drmendel/pictemp_net/firmware/TCPIP/App/GenericTCPServer.c

#define __GENERICTCPSERVER_C

#include "TCPIPConfig.h"

#if defined(STACK_USE_GENERIC_TCP_SERVER_EXAMPLE)

#include "TCPIP Stack/TCPIP.h"
#include "temperature_sensor.h"

// Defines which port the server will listen on
#define SERVER_PORT	2000

void GenericTCPServer(void)
{
	BYTE AppBuffer[32];
    unsigned char TMP_Buffer[TMP_Buffer_Size];           // Buffer to store TMP string
    WORD AB_Length;
	WORD wMaxGet, wMaxPut;
    unsigned int TMP_Inited = 0;
    unsigned int i; 
	static TCP_SOCKET	MySocket;
	static enum _TCPServerState
	{
		SM_HOME = 0,
		SM_LISTENING,
        SM_CLOSING,
	} TCPServerState = SM_HOME;

	switch(TCPServerState)
	{
		case SM_HOME:
			// Allocate a socket for this server to listen and accept connections on
			MySocket = TCPOpen(0, TCP_OPEN_SERVER, SERVER_PORT, TCP_PURPOSE_GENERIC_TCP_SERVER);
			if(MySocket == INVALID_SOCKET) return;
			TCPServerState = SM_LISTENING;
			break;

		case SM_LISTENING:
			// See if anyone is connected to us
			if(!TCPIsConnected(MySocket)) return;
            if(!TMP_Inited)
            {
                TMP_Init();
                TMP_Inited = 1;
            }
            
            // Figure out how many bytes have been received and how many we can transmit.
			wMaxGet = TCPIsGetReady(MySocket);	// Get TCP RX FIFO byte count
			wMaxPut = TCPIsPutReady(MySocket);	// Get TCP TX FIFO free space
    
            if(wMaxGet > 0) // We have incoming data
            {
                // Process all bytes that we can
                WORD Read_Length = (wMaxGet > sizeof(AppBuffer)) ? sizeof(AppBuffer) : wMaxGet;
                AB_Length = TCPGetArray(MySocket, AppBuffer, Read_Length);
                
                
                for(i = 0; i < AB_Length; i++) {
                    
                    if(AppBuffer[i] != 'T' && AppBuffer[i] != 't') {             
                        TCPServerState = SM_CLOSING;
                        break;
                    }
                    // READ the temp sensor 
                    ADC_to_TMP(TMP_Buffer, TMP_Read());
                    // Put the data to the TX buffer
                    //          in this case the package is max. 10 bytes "-40.00 °C\0", "125.00 °C\0"
                    //          we do not need to chunk the buffer to smaller packets
                    TCPPutArray(MySocket, TMP_Buffer, strlen(TMP_Buffer));
                    TCPFlush(MySocket);     // Send data immediately
                }
			}
			break;

		case SM_CLOSING:
			// Close the socket connection.
            TCPClose(MySocket);
			TCPServerState = SM_HOME;
			break;
	}
}

#endif //#if defined(STACK_USE_GENERIC_TCP_SERVER_EXAMPLE)


/*********************************************************************
 *
 *	Generic TCP Server Example Application
 *  Module for Microchip TCP/IP Stack
 *   -Implements an example "ToUpper" TCP server on port 9760 and 
 *	  should be used as a basis for creating new TCP server 
 *    applications
 *
 *********************************************************************
 * FileName:        GenericTCPServer.c
 * Dependencies:    TCP
 * Processor:       PIC18, PIC24F, PIC24H, dsPIC30F, dsPIC33F, PIC32
 * Compiler:        Microchip C32 v1.05 or higher
 *					Microchip C30 v3.12 or higher
 *					Microchip C18 v3.30 or higher
 *					HI-TECH PICC-18 PRO 9.63PL2 or higher
 * Company:         Microchip Technology, Inc.
 *
 * Software License Agreement
 *
 * Copyright (C) 2002-2009 Microchip Technology Inc.  All rights
 * reserved.
 *
 * Microchip licenses to you the right to use, modify, copy, and
 * distribute:
 * (i)  the Software when embedded on a Microchip microcontroller or
 *      digital signal controller product ("Device") which is
 *      integrated into Licensee's product; or
 * (ii) ONLY the Software driver source files ENC28J60.c, ENC28J60.h,
 *		ENCX24J600.c and ENCX24J600.h ported to a non-Microchip device
 *		used in conjunction with a Microchip ethernet controller for
 *		the sole purpose of interfacing with the ethernet controller.
 *
 * You should refer to the license agreement accompanying this
 * Software for additional information regarding your rights and
 * obligations.
 *
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
 *
 * Author               Date    	Comment
 *~~~~~~~~~~~~~~~~~~~~~~~~~~~~~~~~~~~~~~~~~~~~~~~~~~~~~~~~~~~~~~~~~~~~
 * Howard Schlunder     10/19/06	Original
 * Microchip            08/11/10    Added ability to close session by
 *                                  pressing the ESCAPE key.
 *~~~~~~~~~~~~~~~~~~~~~~~~~~~~~~~~~~~~~~~~~~~~~~~~~~~~~~~~~~~~~~~~~~~~
 *
 * Description of how to run the demo:
 *   1) Connect the ethernet port of the programmed demo board to a 
 *        computer either directly or through a router.
 *   2) Determine the IP address of the demo board.  This can be done several
 *        different ways.
 *      a) If you are using a demo setup with an LCD display (e.g. Explorer 16
 *           or PICDEM.net 2), the IP address should be displayed on the second
 *           line of the display.
 *      b) Open the Microchip Ethernet Device Discoverer from the start menu.
 *           Press the "Discover Devices" button to see the addresses and host
 *           names of all devices with the Announce Protocol enabled on your
 *           network.  You may have to configure your computer's firewall to 
 *           prevent it from blocking UDP port 30303 for this solution.
 *      c) If your board is connected directly with your computer with a
 *           crossover cable: 
 *              1) Open a command/DOS prompt and type 'ipconfig'.  Find the 
 *                   network adaptor that is connected to the board.  The IP
 *                   address of the board is located in the 'Default Gateway'
 *                   field
 *              2) Open up the network status for the network adaptor that
 *                   connects the two devices.  This can be done by right clicking
 *                   on the network connection icon in the network settings folder 
 *                   and select 'status' from the menu. Find the 'Default Gateway'
 *                   field.
 *   3) Open a command/DOS prompt.  Type "telnet ip_address 9760" where
 *        ip_address is the IP address that you got from step 2.
 *   4) As you type characters, they will be echoed back in your command prompt
 *        window in UPPER CASE.
 *   5) Press Escape to end the demo.
 *
 ********************************************************************/


/*****************************************************************************
  Function:
	void GenericTCPServer(void)

  Summary:
	Implements a simple ToUpper TCP Server.

  Description:
	This function implements a simple TCP server.  The function is invoked
	periodically by the stack to listen for incoming connections.  When a 
	connection is made, the server reads all incoming data, transforms it
	to uppercase, and echos it back.
	
	This example can be used as a model for many TCP server applications.

  Precondition:
	TCP is initialized.

  Parameters:
	None

  Returns:
  	None
  ***************************************************************************/
