drmendel/pictemp_net/firmware/TCPIP/App/MainDemo.c

/*********************************************************************
 *
 *  Main Application Entry Point and TCP/IP Stack Demo
 *  Module for Microchip TCP/IP Stack
 *   -Demonstrates how to call and use the Microchip TCP/IP stack
 *	 -Reference: Microchip TCP/IP Stack Help (TCPIP Stack Help.chm)
 *
 *********************************************************************
 * FileName:        MainDemo.c
 * Dependencies:    TCPIP.h
 * Processor:       PIC18, PIC24F, PIC24H, dsPIC30F, dsPIC33F, PIC32
 * Compiler:        Microchip C32 v1.11b or higher
 *					Microchip C30 v3.24 or higher
 *					Microchip C18 v3.36 or higher
 * Company:         Microchip Technology, Inc.
 *
 * Software License Agreement
 *
 * Copyright (C) 2002-2010 Microchip Technology Inc.  All rights
 * reserved.
 *
 * Microchip licenses to you the right to use, modify, copy, and
 * distribute:
 * (i)  the Software when embedded on a Microchip microcontroller or
 *      digital signal controller product ("Device") which is
 *      integrated into Licensee's product; or
 * (ii) ONLY the Software driver source files ENC28J60.c, ENC28J60.h,
 *		ENCX24J600.c and ENCX24J600.h ported to a non-Microchip device
 *		used in conjunction with a Microchip ethernet controller for
 *		the sole purpose of interfacing with the ethernet controller.
 *
 * You should refer to the license agreement accompanying this
 * Software for additional information regarding your rights and
 * obligations.
 *
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
 * File Description:
 * Change History:
 * Rev   Description
 * ----  -----------------------------------------
 * 1.0   Initial release
 * V5.36 ---- STACK_USE_MPFS support has been removed 
 ********************************************************************/
/*
 * This macro uniquely defines this file as the main entry point.
 * There should only be one such definition in the entire project,
 * and this file must define the AppConfig variable as described below.
 */
#define THIS_IS_STACK_APPLICATION

// Include all headers for any enabled TCPIP Stack functions
#include "TCPIP Stack/TCPIP.h"

#if defined(STACK_USE_ZEROCONF_LINK_LOCAL)
#include "TCPIP Stack/ZeroconfLinkLocal.h"
#endif
#if defined(STACK_USE_ZEROCONF_MDNS_SD)
#include "TCPIP Stack/ZeroconfMulticastDNS.h"
#endif

// Include functions specific to this stack application
#include "MainDemo.h"

// Used for Wi-Fi assertions
#define WF_MODULE_NUMBER   WF_MODULE_MAIN_DEMO

// Declare AppConfig structure and some other supporting stack variables
APP_CONFIG AppConfig;
static unsigned short wOriginalAppConfigChecksum;	// Checksum of the ROM defaults for AppConfig
BYTE AN0String[8];

// Use UART2 instead of UART1 for stdout (printf functions).  Explorer 16 
// serial port hardware is on PIC UART2 module.
#if defined(EXPLORER_16) || defined(PIC24FJ256DA210_DEV_BOARD)
	int __C30_UART = 2;
#endif


// Private helper functions.
// These may or may not be present in all applications.
static void InitAppConfig(void);
static void InitializeBoard(void);
static void ProcessIO(void);
#if defined(WF_CS_TRIS)
    static void WF_Connect(void);
#endif

//
// PIC18 Interrupt Service Routines
// 
// NOTE: Several PICs, including the PIC18F4620 revision A3 have a RETFIE FAST/MOVFF bug
// The interruptlow keyword is used to work around the bug when using C18
#if defined(__18CXX)
	#if defined(HI_TECH_C)
	void interrupt low_priority LowISR(void)
	#else
	#pragma interruptlow LowISR
	void LowISR(void)
	#endif
	{
	    TickUpdate();
	}
	
	#if defined(HI_TECH_C)
	void interrupt HighISR(void)
	#else
	#pragma interruptlow HighISR
	void HighISR(void)
	#endif
	{
	    #if defined(STACK_USE_UART2TCP_BRIDGE)
			UART2TCPBridgeISR();
		#endif

		#if defined(WF_CS_TRIS)
			WFEintISR();
		#endif // WF_CS_TRIS
	}

	#if !defined(HI_TECH_C)
	#pragma code lowVector=0x18
	void LowVector(void){_asm goto LowISR _endasm}
	#pragma code highVector=0x8
	void HighVector(void){_asm goto HighISR _endasm}
	#pragma code // Return to default code section
	#endif

// C30 and C32 Exception Handlers
// If your code gets here, you either tried to read or write
// a NULL pointer, or your application overflowed the stack
// by having too many local variables or parameters declared.
#elif defined(__C30__)
	void _ISR __attribute__((__no_auto_psv__)) _AddressError(void)
	{
	    Nop();
		Nop();
	}
	void _ISR __attribute__((__no_auto_psv__)) _StackError(void)
	{
	    Nop();
		Nop();
	}
	
#elif defined(__C32__)
	void _general_exception_handler(unsigned cause, unsigned status)
	{
		Nop();
		Nop();
	}
#endif


//
// Main application entry point.
//
#if defined(__18CXX)
void main(void)
#else
int main(void)
#endif
{
	static DWORD t = 0;
	static DWORD dwLastIP = 0;
	#if defined(WF_USE_POWER_SAVE_FUNCTIONS)
	BOOL  PsPollEnabled;
	BOOL  psConfDone = FALSE;
	#endif

	// Initialize application specific hardware
	InitializeBoard();

	#if defined(USE_LCD)
	// Initialize and display the stack version on the LCD
	LCDInit();
	DelayMs(100);
	strcpypgm2ram((char*)LCDText, "TCPStack " TCPIP_STACK_VERSION "  "
		"                ");
	LCDUpdate();
	#endif

	// Initialize stack-related hardware components that may be 
	// required by the UART configuration routines
    TickInit();
	#if defined(STACK_USE_MPFS2)
	MPFSInit();
	#endif

	// Initialize Stack and application related NV variables into AppConfig.
	InitAppConfig();

    // Initiates board setup process if button is depressed 
	// on startup
    if(BUTTON0_IO == 0u)
    {
		#if defined(EEPROM_CS_TRIS) || defined(SPIFLASH_CS_TRIS)
		// Invalidate the EEPROM contents if BUTTON0 is held down for more than 4 seconds
		DWORD StartTime = TickGet();
		LED_PUT(0x00);
				
		while(BUTTON0_IO == 0u)
		{
			if(TickGet() - StartTime > 4*TICK_SECOND)
			{
				#if defined(EEPROM_CS_TRIS)
			    XEEBeginWrite(0x0000);
			    XEEWrite(0xFF);
			    XEEWrite(0xFF);
			    XEEEndWrite();
			    #elif defined(SPIFLASH_CS_TRIS)
			    SPIFlashBeginWrite(0x0000);
			    SPIFlashWrite(0xFF);
			    SPIFlashWrite(0xFF);
			    #endif
			    
				#if defined(STACK_USE_UART)
				putrsUART("\r\n\r\nBUTTON0 held for more than 4 seconds.  Default settings restored.\r\n\r\n");
				#endif

				LED_PUT(0x0F);
				while((LONG)(TickGet() - StartTime) <= (LONG)(9*TICK_SECOND/2));
				LED_PUT(0x00);
				while(BUTTON0_IO == 0u);
				Reset();
				break;
			}
		}
		#endif

		#if defined(STACK_USE_UART)
        DoUARTConfig();
		#endif
    }

	// Initialize core stack layers (MAC, ARP, TCP, UDP) and
	// application modules (HTTP, SNMP, etc.)
    StackInit();

    #if defined(WF_CS_TRIS)
    WF_Connect();
    #endif

	// Initialize any application-specific modules or functions/
	// For this demo application, this only includes the
	// UART 2 TCP Bridge
	#if defined(STACK_USE_UART2TCP_BRIDGE)
	UART2TCPBridgeInit();
	#endif

	#if defined(STACK_USE_ZEROCONF_LINK_LOCAL)
    ZeroconfLLInitialize();
	#endif

	#if defined(STACK_USE_ZEROCONF_MDNS_SD)
	mDNSInitialize(MY_DEFAULT_HOST_NAME);
	mDNSServiceRegister(
		(const char *) "DemoWebServer",	// base name of the service
		"_http._tcp.local",			    // type of the service
		80,				                // TCP or UDP port, at which this service is available
		((const BYTE *)"path=/index.htm"),	// TXT info
		1,								    // auto rename the service when if needed
		NULL,							    // no callback function
		NULL							    // no application context
		);

    mDNSMulticastFilterRegister();			
	#endif

	// Now that all items are initialized, begin the co-operative
	// multitasking loop.  This infinite loop will continuously 
	// execute all stack-related tasks, as well as your own
	// application's functions.  Custom functions should be added
	// at the end of this loop.
    // Note that this is a "co-operative mult-tasking" mechanism
    // where every task performs its tasks (whether all in one shot
    // or part of it) and returns so that other tasks can do their
    // job.
    // If a task needs very long time to do its job, it must be broken
    // down into smaller pieces so that other tasks can have CPU time.    
    
    while(1)
    {
	#if defined(WF_USE_POWER_SAVE_FUNCTIONS)
		if (!psConfDone && WFisConnected()) {	
			PsPollEnabled = (MY_DEFAULT_PS_POLL == WF_ENABLED);
			if (!PsPollEnabled) {	 
				/* disable low power (PS-Poll) mode */
				#if defined(STACK_USE_UART)
				putrsUART("Disable PS-Poll\r\n");		 
				#endif
				WF_PsPollDisable();
			} else {
				/* Enable low power (PS-Poll) mode */
				#if defined(STACK_USE_UART)
				putrsUART("Enable PS-Poll\r\n");		
				#endif
				WF_PsPollEnable(TRUE);
			}	
			psConfDone = TRUE;
		}
	#endif
        // Blink LED0 (right most one) every second.
        if(TickGet() - t >= TICK_SECOND/2ul)
        {
            t = TickGet();
            LED0_IO ^= 1;
        }

        // This task performs normal stack task including checking
        // for incoming packet, type of packet and calling
        // appropriate stack entity to process it.
        StackTask();

        // This tasks invokes each of the core stack application tasks
        StackApplications();

        #if defined(STACK_USE_ZEROCONF_LINK_LOCAL)
		ZeroconfLLProcess();
        #endif

        #if defined(STACK_USE_ZEROCONF_MDNS_SD)
        mDNSProcess();
		// Use this function to exercise service update function
		// HTTPUpdateRecord();
        #endif

		// Process application specific tasks here.
		// For this demo app, this will include the Generic TCP 
		// client and servers, and the SNMP, Ping, and SNMP Trap
		// demos.  Following that, we will process any IO from
		// the inputs on the board itself.
		// Any custom modules or processing you need to do should
		// go here.
		#if defined(STACK_USE_GENERIC_TCP_CLIENT_EXAMPLE)
		GenericTCPClient();
		#endif
		
		#if defined(STACK_USE_GENERIC_TCP_SERVER_EXAMPLE)
		GenericTCPServer();
		#endif
		
		#if defined(STACK_USE_SMTP_CLIENT)
		SMTPDemo();
		#endif
		
		#if defined(STACK_USE_ICMP_CLIENT)
		PingDemo();
		#endif
		
		#if defined(STACK_USE_SNMP_SERVER) && !defined(SNMP_TRAP_DISABLED)
		//User should use one of the following SNMP demo
		// This routine demonstrates V1 or V2 trap formats with one variable binding.
		SNMPTrapDemo();
		
		#if defined(SNMP_STACK_USE_V2_TRAP) || defined(SNMP_V1_V2_TRAP_WITH_SNMPV3)
		//This routine provides V2 format notifications with multiple (3) variable bindings
		//User should modify this routine to send v2 trap format notifications with the required varbinds.
		//SNMPV2TrapDemo();
		#endif 
		if(gSendTrapFlag)
			SNMPSendTrap();
		#endif
		
		#if defined(STACK_USE_BERKELEY_API)
		BerkeleyTCPClientDemo();
		BerkeleyTCPServerDemo();
		BerkeleyUDPClientDemo();
		#endif

		ProcessIO();

        // If the local IP address has changed (ex: due to DHCP lease change)
        // write the new IP address to the LCD display, UART, and Announce 
        // service
		if(dwLastIP != AppConfig.MyIPAddr.Val)
		{
			dwLastIP = AppConfig.MyIPAddr.Val;
			
			#if defined(STACK_USE_UART)
				putrsUART((ROM char*)"\r\nNew IP Address: ");
			#endif

			DisplayIPValue(AppConfig.MyIPAddr);

			#if defined(STACK_USE_UART)
				putrsUART((ROM char*)"\r\n");
			#endif


			#if defined(STACK_USE_ANNOUNCE)
				AnnounceIP();
			#endif

            #if defined(STACK_USE_ZEROCONF_MDNS_SD)
				mDNSFillHostRecord();
			#endif
		}
	}
}

#if defined(WF_CS_TRIS)
/*****************************************************************************
 * FUNCTION: WF_Connect
 *
 * RETURNS:  None
 *
 * PARAMS:   None
 *
 *  NOTES:   Connects to an 802.11 network.  Customize this function as needed 
 *           for your application.
 *****************************************************************************/
static void WF_Connect(void)
{
    UINT8 ConnectionProfileID;
    UINT8 channelList[] = MY_DEFAULT_CHANNEL_LIST;
    
    /* create a Connection Profile */
    WF_CPCreate(&ConnectionProfileID);

    #if defined(STACK_USE_UART)
    putrsUART("Set SSID (");
    putsUART(AppConfig.MySSID);
    putrsUART(")\r\n");
    #endif
    WF_CPSetSsid(ConnectionProfileID, 
                 AppConfig.MySSID, 
                 AppConfig.SsidLength);

    #if defined(STACK_USE_UART)
    putrsUART("Set Network Type\r\n");
	#endif
    WF_CPSetNetworkType(ConnectionProfileID, MY_DEFAULT_NETWORK_TYPE);
    
	#if defined(STACK_USE_UART)
	putrsUART("Set Scan Type\r\n");
	#endif
    WF_CASetScanType(MY_DEFAULT_SCAN_TYPE);
    
    #if defined(STACK_USE_UART)
    putrsUART("Set Channel List\r\n");
    #endif    
    WF_CASetChannelList(channelList, sizeof(channelList));
    
    #if defined(STACK_USE_UART)
    putrsUART("Set list retry count\r\n");
    #endif
    // The Retry Count parameter tells the WiFi Connection manager how many attempts to make when trying
    // to connect to an existing network.  In the Infrastructure case, the default is to retry forever so that
    // if the AP is turned off or out of range, the radio will continue to attempt a connection until the
    // AP is eventually back on or in range.  In the Adhoc case, the default is to retry 3 times since the 
    // purpose of attempting to establish a network in the Adhoc case is only to verify that one does not
    // initially exist.  If the retry count was set to WF_RETRY_FOREVER in the AdHoc mode, an AdHoc network
    // would never be established.  The constants MY_DEFAULT_LIST_RETRY_COUNT_ADHOC and 
    // MY_DEFAULT_LIST_RETRY_COUNT_INFRASTRUCTURE have been created specifically for the June 2011 MAL release.
    #if defined(EZ_CONFIG_STORE)
        if (AppConfig.networkType == WF_ADHOC)
            WF_CASetListRetryCount(MY_DEFAULT_LIST_RETRY_COUNT_ADHOC);
        else
            WF_CASetListRetryCount(MY_DEFAULT_LIST_RETRY_COUNT_INFRASTRUCTURE);
    #else
        #if (MY_DEFAULT_NETWORK_TYPE == WF_ADHOC)
            WF_CASetListRetryCount(MY_DEFAULT_LIST_RETRY_COUNT_ADHOC);
        #else
            WF_CASetListRetryCount(MY_DEFAULT_LIST_RETRY_COUNT_INFRASTRUCTURE);
        #endif
    #endif
    

    #if defined(STACK_USE_UART)        
    putrsUART("Set Event Notify\r\n");    
    #endif
    WF_CASetEventNotificationAction(MY_DEFAULT_EVENT_NOTIFICATION_LIST);
    
    #if defined(STACK_USE_UART)
    putrsUART("Set Beacon Timeout\r\n");
    #endif
    WF_CASetBeaconTimeout(40);
    
    /* Set Security */
    #if (MY_DEFAULT_WIFI_SECURITY_MODE == WF_SECURITY_OPEN)
        #if defined(STACK_USE_UART)
        putrsUART("Set Security (Open)\r\n");
        #endif
    #elif (MY_DEFAULT_WIFI_SECURITY_MODE == WF_SECURITY_WEP_40)
        #if defined(STACK_USE_UART)
        putrsUART("Set Security (WEP40)\r\n");
        #endif
    #elif (MY_DEFAULT_WIFI_SECURITY_MODE == WF_SECURITY_WEP_104)
        #if defined(STACK_USE_UART)
        putrsUART("Set Security (WEP104)\r\n");
        #endif
    #elif MY_DEFAULT_WIFI_SECURITY_MODE == WF_SECURITY_WPA_WITH_KEY 
        #if defined(STACK_USE_UART)
        putrsUART("Set Security (WPA with key)\r\n");
        #endif
    #elif MY_DEFAULT_WIFI_SECURITY_MODE == WF_SECURITY_WPA2_WITH_KEY 
        #if defined(STACK_USE_UART)
        putrsUART("Set Security (WPA2 with key)\r\n");
        #endif
    #elif MY_DEFAULT_WIFI_SECURITY_MODE == WF_SECURITY_WPA_WITH_PASS_PHRASE
        #if defined(STACK_USE_UART)
        putrsUART("Set Security (WPA with pass phrase)\r\n");
        #endif
    #elif MY_DEFAULT_WIFI_SECURITY_MODE == WF_SECURITY_WPA2_WITH_PASS_PHRASE
        #if defined(STACK_USE_UART)
        putrsUART("Set Security (WPA2 with pass phrase)\r\n");    
        #endif
    #elif MY_DEFAULT_WIFI_SECURITY_MODE == WF_SECURITY_WPA_AUTO_WITH_KEY
        #if defined(STACK_USE_UART)
        putrsUART("Set Security (WPA with key, auto-select)\r\n");
        #endif
    #elif MY_DEFAULT_WIFI_SECURITY_MODE == WF_SECURITY_WPA_AUTO_WITH_PASS_PHRASE
        #if defined(STACK_USE_UART)
        putrsUART("Set Security (WPA with pass phrase, auto-select)\r\n");
        #endif
    #endif /* MY_DEFAULT_WIFI_SECURITY_MODE */

    WF_CPSetSecurity(ConnectionProfileID,
                     AppConfig.SecurityMode,
                     AppConfig.WepKeyIndex,   /* only used if WEP enabled */
                     AppConfig.SecurityKey,
                     AppConfig.SecurityKeyLength);
    #if defined(STACK_USE_UART)                     
    putrsUART("Start WiFi Connect\r\n");        
    #endif
    WF_CMConnect(ConnectionProfileID);
}   
#endif /* WF_CS_TRIS */

// Writes an IP address to the LCD display and the UART as available
void DisplayIPValue(IP_ADDR IPVal)
{
//	printf("%u.%u.%u.%u", IPVal.v[0], IPVal.v[1], IPVal.v[2], IPVal.v[3]);
#if defined (__dsPIC33E__) || defined (__PIC24E__)
	static BYTE IPDigit[4];    					/* Needs to be declared as static to avoid the array getting optimized by C30 v3.30 compiler for dsPIC33E/PIC24E. 
												   Otherwise the LCD displays corrupted IP address on Explorer 16. To be fixed in the future compiler release*/
#else
    BYTE IPDigit[4];
#endif
	BYTE i;
#ifdef USE_LCD
	BYTE j;
	BYTE LCDPos=16;
#endif

	for(i = 0; i < sizeof(IP_ADDR); i++)
	{
	    uitoa((WORD)IPVal.v[i], IPDigit);

		#if defined(STACK_USE_UART)
			putsUART((char *) IPDigit);
		#endif

		#ifdef USE_LCD
			for(j = 0; j < strlen((char*)IPDigit); j++)
			{
				LCDText[LCDPos++] = IPDigit[j];
			}
			if(i == sizeof(IP_ADDR)-1)
				break;
			LCDText[LCDPos++] = '.';
		#else
			if(i == sizeof(IP_ADDR)-1)
				break;
		#endif

		#if defined(STACK_USE_UART)
			while(BusyUART());
			WriteUART('.');
		#endif
	}

	#ifdef USE_LCD
		if(LCDPos < 32u)
			LCDText[LCDPos] = 0;
		LCDUpdate();
	#endif
}

// Processes A/D data from the potentiometer
static void ProcessIO(void)
{
#if defined(__C30__) || defined(__C32__)
    // Convert potentiometer result into ASCII string
    uitoa((WORD)ADC1BUF0, AN0String);
#else
    // AN0 should already be set up as an analog input
    ADCON0bits.GO = 1;

    // Wait until A/D conversion is done
    while(ADCON0bits.GO);

	// AD converter errata work around (ex: PIC18F87J10 A2)
	#if !defined(__18F87J50) && !defined(_18F87J50) && !defined(__18F87J11) && !defined(_18F87J11) 
	{
		BYTE temp = ADCON2;
		ADCON2 |= 0x7;	// Select Frc mode by setting ADCS0/ADCS1/ADCS2
		ADCON2 = temp;
	}
	#endif

    // Convert 10-bit value into ASCII string
    uitoa(*((WORD*)(&ADRESL)), AN0String);
#endif
}


/****************************************************************************
  Function:
    static void InitializeBoard(void)

  Description:
    This routine initializes the hardware.  It is a generic initialization
    routine for many of the Microchip development boards, using definitions
    in HardwareProfile.h to determine specific initialization.

  Precondition:
    None

  Parameters:
    None - None

  Returns:
    None

  Remarks:
    None
  ***************************************************************************/
static void InitializeBoard(void)
{	
	// LEDs
	LED0_TRIS = 0;
	LED1_TRIS = 0;
	LED2_TRIS = 0;
	LED3_TRIS = 0;
	LED4_TRIS = 0;
	LED5_TRIS = 0;
	LED6_TRIS = 0;
	LED7_TRIS = 0;
	LED_PUT(0x00);

#if defined(__18CXX)
	// Enable 4x/5x/96MHz PLL on PIC18F87J10, PIC18F97J60, PIC18F87J50, etc.
    OSCTUNE = 0x40;

	// Set up analog features of PORTA

	// PICDEM.net 2 board has POT on AN2, Temp Sensor on AN3
	#if defined(PICDEMNET2)
		ADCON0 = 0x09;		// ADON, Channel 2
		ADCON1 = 0x0B;		// Vdd/Vss is +/-REF, AN0, AN1, AN2, AN3 are analog
	#elif defined(PICDEMZ)
		ADCON0 = 0x81;		// ADON, Channel 0, Fosc/32
		ADCON1 = 0x0F;		// Vdd/Vss is +/-REF, AN0, AN1, AN2, AN3 are all digital
	#elif defined(__18F87J11) || defined(_18F87J11) || defined(__18F87J50) || defined(_18F87J50)
		ADCON0 = 0x01;		// ADON, Channel 0, Vdd/Vss is +/-REF
		WDTCONbits.ADSHR = 1;
		ANCON0 = 0xFC;		// AN0 (POT) and AN1 (temp sensor) are anlog
		ANCON1 = 0xFF;
		WDTCONbits.ADSHR = 0;		
	#else
		ADCON0 = 0x01;		// ADON, Channel 0
		ADCON1 = 0x0E;		// Vdd/Vss is +/-REF, AN0 is analog
	#endif
	ADCON2 = 0xBE;		// Right justify, 20TAD ACQ time, Fosc/64 (~21.0kHz)


    // Enable internal PORTB pull-ups
    INTCON2bits.RBPU = 0;

	// Configure USART
    TXSTA = 0x20;
    RCSTA = 0x90;

	// See if we can use the high baud rate setting
	#if ((GetPeripheralClock()+2*BAUD_RATE)/BAUD_RATE/4 - 1) <= 255
		SPBRG = (GetPeripheralClock()+2*BAUD_RATE)/BAUD_RATE/4 - 1;
		TXSTAbits.BRGH = 1;
	#else	// Use the low baud rate setting
		SPBRG = (GetPeripheralClock()+8*BAUD_RATE)/BAUD_RATE/16 - 1;
	#endif


	// Enable Interrupts
	RCONbits.IPEN = 1;		// Enable interrupt priorities
    INTCONbits.GIEH = 1;
    INTCONbits.GIEL = 1;

    // Do a calibration A/D conversion
	#if defined(__18F87J10) || defined(__18F86J15) || defined(__18F86J10) || defined(__18F85J15) || defined(__18F85J10) || defined(__18F67J10) || defined(__18F66J15) || defined(__18F66J10) || defined(__18F65J15) || defined(__18F65J10) || defined(__18F97J60) || defined(__18F96J65) || defined(__18F96J60) || defined(__18F87J60) || defined(__18F86J65) || defined(__18F86J60) || defined(__18F67J60) || defined(__18F66J65) || defined(__18F66J60) || \
	     defined(_18F87J10) ||  defined(_18F86J15) || defined(_18F86J10)  ||  defined(_18F85J15) ||  defined(_18F85J10) ||  defined(_18F67J10) ||  defined(_18F66J15) ||  defined(_18F66J10) ||  defined(_18F65J15) ||  defined(_18F65J10) ||  defined(_18F97J60) ||  defined(_18F96J65) ||  defined(_18F96J60) ||  defined(_18F87J60) ||  defined(_18F86J65) ||  defined(_18F86J60) ||  defined(_18F67J60) ||  defined(_18F66J65) ||  defined(_18F66J60)
		ADCON0bits.ADCAL = 1;
	    ADCON0bits.GO = 1;
		while(ADCON0bits.GO);
		ADCON0bits.ADCAL = 0;
	#elif defined(__18F87J11) || defined(__18F86J16) || defined(__18F86J11) || defined(__18F67J11) || defined(__18F66J16) || defined(__18F66J11) || \
		   defined(_18F87J11) ||  defined(_18F86J16) ||  defined(_18F86J11) ||  defined(_18F67J11) ||  defined(_18F66J16) ||  defined(_18F66J11) || \
		  defined(__18F87J50) || defined(__18F86J55) || defined(__18F86J50) || defined(__18F67J50) || defined(__18F66J55) || defined(__18F66J50) || \
		   defined(_18F87J50) ||  defined(_18F86J55) ||  defined(_18F86J50) ||  defined(_18F67J50) ||  defined(_18F66J55) ||  defined(_18F66J50)
		ADCON1bits.ADCAL = 1;
	    ADCON0bits.GO = 1;
		while(ADCON0bits.GO);
		ADCON1bits.ADCAL = 0;
	#endif

#else	// 16-bit C30 and and 32-bit C32
	#if defined(__PIC32MX__)
	{
		// Enable multi-vectored interrupts
		INTEnableSystemMultiVectoredInt();
		
		// Enable optimal performance
		SYSTEMConfigPerformance(GetSystemClock());
		mOSCSetPBDIV(OSC_PB_DIV_1);				// Use 1:1 CPU Core:Peripheral clocks
		
		// Disable JTAG port so we get our I/O pins back, but first
		// wait 50ms so if you want to reprogram the part with 
		// JTAG, you'll still have a tiny window before JTAG goes away.
		// The PIC32 Starter Kit debuggers use JTAG and therefore must not 
		// disable JTAG.
		DelayMs(50);
		#if !defined(__MPLAB_DEBUGGER_PIC32MXSK) && !defined(__MPLAB_DEBUGGER_FS2)
			DDPCONbits.JTAGEN = 0;
		#endif
		LED_PUT(0x00);				// Turn the LEDs off
		
		CNPUESET = 0x00098000;		// Turn on weak pull ups on CN15, CN16, CN19 (RD5, RD7, RD13), which is connected to buttons on PIC32 Starter Kit boards
	}
	#endif

	#if defined(__dsPIC33F__) || defined(__PIC24H__)
		// Crank up the core frequency
		PLLFBD = 38;				// Multiply by 40 for 160MHz VCO output (8MHz XT oscillator)
		CLKDIV = 0x0000;			// FRC: divide by 2, PLLPOST: divide by 2, PLLPRE: divide by 2
	
		// Port I/O
		AD1PCFGHbits.PCFG23 = 1;	// Make RA7 (BUTTON1) a digital input
		AD1PCFGHbits.PCFG20 = 1;	// Make RA12 (INT1) a digital input for MRF24WB0M PICtail Plus interrupt

		// ADC
	    AD1CHS0 = 0;				// Input to AN0 (potentiometer)
		AD1PCFGLbits.PCFG5 = 0;		// Disable digital input on AN5 (potentiometer)
		AD1PCFGLbits.PCFG4 = 0;		// Disable digital input on AN4 (TC1047A temp sensor)


	#elif defined(__dsPIC33E__)||defined(__PIC24E__)

		// Crank up the core frequency
		PLLFBD = 38;				/* M  = 30	*/
		CLKDIVbits.PLLPOST = 0;		/* N1 = 2	*/
		CLKDIVbits.PLLPRE = 0;		/* N2 = 2	*/
		OSCTUN = 0;	
		
	    /*	Initiate Clock Switch to Primary
	     *	Oscillator with PLL (NOSC= 0x3)*/
	    __builtin_write_OSCCONH(0x03);		
		__builtin_write_OSCCONL(0x01);
		// Disable Watch Dog Timer
	    RCONbits.SWDTEN = 0;
		while (OSCCONbits.COSC != 0x3); 
		while (_LOCK == 0);			/* Wait for PLL lock at 60 MIPS */		
		// Port I/O
		ANSELAbits.ANSA7 = 0 ;   //Make RA7 (BUTTON1) a digital input
		#if defined ENC100_INTERFACE_MODE > 0
			ANSELEbits.ANSE0 = 0;      // Make these PMP pins as digital output when the interface is parallel.
			ANSELEbits.ANSE1 = 0;
			ANSELEbits.ANSE2 = 0;
			ANSELEbits.ANSE3 = 0;	
			ANSELEbits.ANSE4 = 0;
			ANSELEbits.ANSE5 = 0;
			ANSELEbits.ANSE6 = 0;
			ANSELEbits.ANSE7 = 0;	
			ANSELBbits.ANSB10 = 0;
			ANSELBbits.ANSB11 = 0;
			ANSELBbits.ANSB12 = 0;
			ANSELBbits.ANSB13 = 0;
			ANSELBbits.ANSB15 = 0;
		#endif

		ANSELEbits.ANSE8= 0 ;    // Make RE8(INT1) a digital input for ZeroG ZG2100M PICtail 
					
		AD1CHS0 = 0;		     // Input to AN0 (potentiometer)
		ANSELBbits.ANSB0= 1;     // Input to AN0 (potentiometer)
		ANSELBbits.ANSB5= 1;     // Disable digital input on AN5 (potentiometer)
		ANSELBbits.ANSB4= 1;     // Disable digital input on AN4 (TC1047A temp sensor)
					
		ANSELDbits.ANSD7 =0;     //  Digital Pin Selection for S3(Pin 83) and S4(pin 84).
		ANSELDbits.ANSD6 =0;
			
		ANSELGbits.ANSG6 =0;     // Enable Digital input for RG6 (SCK2)
		ANSELGbits.ANSG7 =0;     // Enable Digital input for RG7 (SDI2)
		ANSELGbits.ANSG8 =0;     // Enable Digital input for RG8 (SDO2)
		ANSELGbits.ANSG9 =0;     // Enable Digital input for RG9 (CS)
				
		#if defined ENC100_INTERFACE_MODE == 0	// SPI Interface, UART can be used for debugging. Not allowed for other interfaces.
			RPOR9 = 0x0300;          //RP101= U2TX
			RPINR19 = 0X0064;  		 //RP100= U2RX
		#endif

		#if defined WF_CS_TRIS
			RPINR1bits.INT3R = 30;
			WF_CS_IO = 1;
			WF_CS_TRIS = 0;		

		#endif

	#else	//defined(__PIC24F__) || defined(__PIC32MX__)
		#if defined(__PIC24F__)
			CLKDIVbits.RCDIV = 0;		// Set 1:1 8MHz FRC postscalar
		#endif
		
		// ADC
	    #if defined(__PIC24FJ256DA210__) || defined(__PIC24FJ256GB210__)
	    	// Disable analog on all pins
	    	ANSA = 0x0000;
	    	ANSB = 0x0000;
	    	ANSC = 0x0000;
	    	ANSD = 0x0000;
	    	ANSE = 0x0000;
	    	ANSF = 0x0000;
	    	ANSG = 0x0000;
		#else
		    AD1CHS = 0;					// Input to AN0 (potentiometer)
			AD1PCFGbits.PCFG4 = 0;		// Disable digital input on AN4 (TC1047A temp sensor)
			#if defined(__32MX460F512L__) || defined(__32MX795F512L__)	// PIC32MX460F512L and PIC32MX795F512L PIMs has different pinout to accomodate USB module
				AD1PCFGbits.PCFG2 = 0;		// Disable digital input on AN2 (potentiometer)
			#else
				AD1PCFGbits.PCFG5 = 0;		// Disable digital input on AN5 (potentiometer)
			#endif
		#endif
	#endif

	// ADC
	AD1CON1 = 0x84E4;			// Turn on, auto sample start, auto-convert, 12 bit mode (on parts with a 12bit A/D)
	AD1CON2 = 0x0404;			// AVdd, AVss, int every 2 conversions, MUXA only, scan
	AD1CON3 = 0x1003;			// 16 Tad auto-sample, Tad = 3*Tcy
	#if defined(__32MX460F512L__) || defined(__32MX795F512L__)	// PIC32MX460F512L and PIC32MX795F512L PIMs has different pinout to accomodate USB module
		AD1CSSL = 1<<2;				// Scan pot
	#else
		AD1CSSL = 1<<5;				// Scan pot
	#endif

	// UART
	#if defined(STACK_USE_UART)

		#if defined(__PIC24E__) || defined(__dsPIC33E__)
			#if defined (ENC_CS_IO) || defined (WF_CS_IO)   // UART to be used in case of ENC28J60 or MRF24WB0M
				__builtin_write_OSCCONL(OSCCON & 0xbf);
				RPOR9bits.RP101R = 3; //Map U2TX to RF5
				RPINR19bits.U2RXR = 0;
				RPINR19bits.U2RXR = 0x64; //Map U2RX to RF4
				__builtin_write_OSCCONL(OSCCON | 0x40);
			#endif
			#if(ENC100_INTERFACE_MODE == 0)                 // UART to be used only in case of SPI interface with ENC624Jxxx
					__builtin_write_OSCCONL(OSCCON & 0xbf);
				RPOR9bits.RP101R = 3; //Map U2TX to RF5
				RPINR19bits.U2RXR = 0;
				RPINR19bits.U2RXR = 0x64; //Map U2RX to RF4
				__builtin_write_OSCCONL(OSCCON | 0x40);

			#endif
		#endif

		UARTTX_TRIS = 0;
		UARTRX_TRIS = 1;
		UMODE = 0x8000;			// Set UARTEN.  Note: this must be done before setting UTXEN

		#if defined(__C30__)
			USTA = 0x0400;		// UTXEN set
			#define CLOSEST_UBRG_VALUE ((GetPeripheralClock()+8ul*BAUD_RATE)/16/BAUD_RATE-1)
			#define BAUD_ACTUAL (GetPeripheralClock()/16/(CLOSEST_UBRG_VALUE+1))
		#else	//defined(__C32__)
			USTA = 0x00001400;		// RXEN set, TXEN set
			#define CLOSEST_UBRG_VALUE ((GetPeripheralClock()+8ul*BAUD_RATE)/16/BAUD_RATE-1)
			#define BAUD_ACTUAL (GetPeripheralClock()/16/(CLOSEST_UBRG_VALUE+1))
		#endif
	
		#define BAUD_ERROR ((BAUD_ACTUAL > BAUD_RATE) ? BAUD_ACTUAL-BAUD_RATE : BAUD_RATE-BAUD_ACTUAL)
		#define BAUD_ERROR_PRECENT	((BAUD_ERROR*100+BAUD_RATE/2)/BAUD_RATE)
		#if (BAUD_ERROR_PRECENT > 3)
			#warning UART frequency error is worse than 3%
		#elif (BAUD_ERROR_PRECENT > 2)
			#warning UART frequency error is worse than 2%
		#endif
	
		UBRG = CLOSEST_UBRG_VALUE;
	#endif

#endif

// Deassert all chip select lines so there isn't any problem with 
// initialization order.  Ex: When ENC28J60 is on SPI2 with Explorer 16, 
// MAX3232 ROUT2 pin will drive RF12/U2CTS ENC28J60 CS line asserted, 
// preventing proper 25LC256 EEPROM operation.
#if defined(ENC_CS_TRIS)
	ENC_CS_IO = 1;
	ENC_CS_TRIS = 0;
#endif
#if defined(ENC100_CS_TRIS)
	ENC100_CS_IO = (ENC100_INTERFACE_MODE == 0);
	ENC100_CS_TRIS = 0;
#endif
#if defined(EEPROM_CS_TRIS)
	EEPROM_CS_IO = 1;
	EEPROM_CS_TRIS = 0;
#endif
#if defined(SPIRAM_CS_TRIS)
	SPIRAM_CS_IO = 1;
	SPIRAM_CS_TRIS = 0;
#endif
#if defined(SPIFLASH_CS_TRIS)
	SPIFLASH_CS_IO = 1;
	SPIFLASH_CS_TRIS = 0;
#endif
#if defined(WF_CS_TRIS)
	WF_CS_IO = 1;
	WF_CS_TRIS = 0;
#endif

#if defined(PIC24FJ64GA004_PIM)
	__builtin_write_OSCCONL(OSCCON & 0xBF);  // Unlock PPS

	// Remove some LED outputs to regain other functions
	LED1_TRIS = 1;		// Multiplexed with BUTTON0
	LED5_TRIS = 1;		// Multiplexed with EEPROM CS
	LED7_TRIS = 1;		// Multiplexed with BUTTON1
	
	// Inputs
	RPINR19bits.U2RXR = 19;			//U2RX = RP19
	RPINR22bits.SDI2R = 20;			//SDI2 = RP20
	RPINR20bits.SDI1R = 17;			//SDI1 = RP17
	
	// Outputs
	RPOR12bits.RP25R = U2TX_IO;		//RP25 = U2TX  
	RPOR12bits.RP24R = SCK2OUT_IO; 	//RP24 = SCK2
	RPOR10bits.RP21R = SDO2_IO;		//RP21 = SDO2
	RPOR7bits.RP15R = SCK1OUT_IO; 	//RP15 = SCK1
	RPOR8bits.RP16R = SDO1_IO;		//RP16 = SDO1
	
	AD1PCFG = 0xFFFF;				//All digital inputs - POT and Temp are on same pin as SDO1/SDI1, which is needed for ENC28J60 commnications

	__builtin_write_OSCCONL(OSCCON | 0x40); // Lock PPS
#endif

#if defined(__PIC24FJ256DA210__)
	__builtin_write_OSCCONL(OSCCON & 0xBF);  // Unlock PPS

	// Inputs
	RPINR19bits.U2RXR = 11;	// U2RX = RP11
	RPINR20bits.SDI1R = 0;	// SDI1 = RP0
	RPINR0bits.INT1R = 34;	// Assign RE9/RPI34 to INT1 (input) for MRF24WB0M Wi-Fi PICtail Plus interrupt
	
	// Outputs
	RPOR8bits.RP16R = 5;	// RP16 = U2TX
	RPOR1bits.RP2R = 8; 	// RP2 = SCK1
	RPOR0bits.RP1R = 7;		// RP1 = SDO1

	__builtin_write_OSCCONL(OSCCON | 0x40); // Lock PPS
#endif

#if defined(__PIC24FJ256GB110__) || defined(__PIC24FJ256GB210__)
	__builtin_write_OSCCONL(OSCCON & 0xBF);  // Unlock PPS
	
	// Configure SPI1 PPS pins (ENC28J60/ENCX24J600/MRF24WB0M or other PICtail Plus cards)
	RPOR0bits.RP0R = 8;		// Assign RP0 to SCK1 (output)
	RPOR7bits.RP15R = 7;	// Assign RP15 to SDO1 (output)
	RPINR20bits.SDI1R = 23;	// Assign RP23 to SDI1 (input)

	// Configure SPI2 PPS pins (25LC256 EEPROM on Explorer 16)
	RPOR10bits.RP21R = 11;	// Assign RG6/RP21 to SCK2 (output)
	RPOR9bits.RP19R = 10;	// Assign RG8/RP19 to SDO2 (output)
	RPINR22bits.SDI2R = 26;	// Assign RG7/RP26 to SDI2 (input)
	
	// Configure UART2 PPS pins (MAX3232 on Explorer 16)
	#if !defined(ENC100_INTERFACE_MODE) || (ENC100_INTERFACE_MODE == 0) || defined(ENC100_PSP_USE_INDIRECT_RAM_ADDRESSING)
	RPINR19bits.U2RXR = 10;	// Assign RF4/RP10 to U2RX (input)
	RPOR8bits.RP17R = 5;	// Assign RF5/RP17 to U2TX (output)
	#endif
	
	// Configure INT1 PPS pin (MRF24WB0M Wi-Fi PICtail Plus interrupt signal when in SPI slot 1)
	RPINR0bits.INT1R = 33;	// Assign RE8/RPI33 to INT1 (input)

	// Configure INT3 PPS pin (MRF24WB0M Wi-Fi PICtail Plus interrupt signal when in SPI slot 2)
	RPINR1bits.INT3R = 40;	// Assign RC3/RPI40 to INT3 (input)

	__builtin_write_OSCCONL(OSCCON | 0x40); // Lock PPS
#endif

#if defined(__PIC24FJ256GA110__)
	__builtin_write_OSCCONL(OSCCON & 0xBF);  // Unlock PPS
	
	// Configure SPI2 PPS pins (25LC256 EEPROM on Explorer 16 and ENC28J60/ENCX24J600/MRF24WB0M or other PICtail Plus cards)
	// Note that the ENC28J60/ENCX24J600/MRF24WB0M PICtails SPI PICtails must be inserted into the middle SPI2 socket, not the topmost SPI1 slot as normal.  This is because PIC24FJ256GA110 A3 silicon has an input-only RPI PPS pin in the ordinary SCK1 location.  Silicon rev A5 has this fixed, but for simplicity all demos will assume we are using SPI2.
	RPOR10bits.RP21R = 11;	// Assign RG6/RP21 to SCK2 (output)
	RPOR9bits.RP19R = 10;	// Assign RG8/RP19 to SDO2 (output)
	RPINR22bits.SDI2R = 26;	// Assign RG7/RP26 to SDI2 (input)
	
	// Configure UART2 PPS pins (MAX3232 on Explorer 16)
	RPINR19bits.U2RXR = 10;	// Assign RF4/RP10 to U2RX (input)
	RPOR8bits.RP17R = 5;	// Assign RF5/RP17 to U2TX (output)
	
	// Configure INT3 PPS pin (MRF24WB0M PICtail Plus interrupt signal)
	RPINR1bits.INT3R = 36;	// Assign RA14/RPI36 to INT3 (input)

	__builtin_write_OSCCONL(OSCCON | 0x40); // Lock PPS
#endif


#if defined(DSPICDEM11)
	// Deselect the LCD controller (PIC18F252 onboard) to ensure there is no SPI2 contention
	LCDCTRL_CS_TRIS = 0;
	LCDCTRL_CS_IO = 1;

	// Hold the codec in reset to ensure there is no SPI2 contention
	CODEC_RST_TRIS = 0;
	CODEC_RST_IO = 0;
#endif

#if defined(SPIRAM_CS_TRIS)
	SPIRAMInit();
#endif
#if defined(EEPROM_CS_TRIS)
	XEEInit();
#endif
#if defined(SPIFLASH_CS_TRIS)
	SPIFlashInit();
#endif
}

/*********************************************************************
 * Function:        void InitAppConfig(void)
 *
 * PreCondition:    MPFSInit() is already called.
 *
 * Input:           None
 *
 * Output:          Write/Read non-volatile config variables.
 *
 * Side Effects:    None
 *
 * Overview:        None
 *
 * Note:            None
 ********************************************************************/
// MAC Address Serialization using a MPLAB PM3 Programmer and 
// Serialized Quick Turn Programming (SQTP). 
// The advantage of using SQTP for programming the MAC Address is it
// allows you to auto-increment the MAC address without recompiling 
// the code for each unit.  To use SQTP, the MAC address must be fixed
// at a specific location in program memory.  Uncomment these two pragmas
// that locate the MAC address at 0x1FFF0.  Syntax below is for MPLAB C 
// Compiler for PIC18 MCUs. Syntax will vary for other compilers.
//#pragma romdata MACROM=0x1FFF0
static ROM BYTE SerializedMACAddress[6] = {MY_DEFAULT_MAC_BYTE1, MY_DEFAULT_MAC_BYTE2, MY_DEFAULT_MAC_BYTE3, MY_DEFAULT_MAC_BYTE4, MY_DEFAULT_MAC_BYTE5, MY_DEFAULT_MAC_BYTE6};
//#pragma romdata

static void InitAppConfig(void)
{
#if defined(EEPROM_CS_TRIS) || defined(SPIFLASH_CS_TRIS)
	unsigned char vNeedToSaveDefaults = 0;
#endif
	
	while(1)
	{
		// Start out zeroing all AppConfig bytes to ensure all fields are 
		// deterministic for checksum generation
		memset((void*)&AppConfig, 0x00, sizeof(AppConfig));
		
		AppConfig.Flags.bIsDHCPEnabled = TRUE;
		AppConfig.Flags.bInConfigMode = TRUE;
		memcpypgm2ram((void*)&AppConfig.MyMACAddr, (ROM void*)SerializedMACAddress, sizeof(AppConfig.MyMACAddr));
//		{
//			_prog_addressT MACAddressAddress;
//			MACAddressAddress.next = 0x157F8;
//			_memcpy_p2d24((char*)&AppConfig.MyMACAddr, MACAddressAddress, sizeof(AppConfig.MyMACAddr));
//		}
		AppConfig.MyIPAddr.Val = MY_DEFAULT_IP_ADDR_BYTE1 | MY_DEFAULT_IP_ADDR_BYTE2<<8ul | MY_DEFAULT_IP_ADDR_BYTE3<<16ul | MY_DEFAULT_IP_ADDR_BYTE4<<24ul;
		AppConfig.DefaultIPAddr.Val = AppConfig.MyIPAddr.Val;
		AppConfig.MyMask.Val = MY_DEFAULT_MASK_BYTE1 | MY_DEFAULT_MASK_BYTE2<<8ul | MY_DEFAULT_MASK_BYTE3<<16ul | MY_DEFAULT_MASK_BYTE4<<24ul;
		AppConfig.DefaultMask.Val = AppConfig.MyMask.Val;
		AppConfig.MyGateway.Val = MY_DEFAULT_GATE_BYTE1 | MY_DEFAULT_GATE_BYTE2<<8ul | MY_DEFAULT_GATE_BYTE3<<16ul | MY_DEFAULT_GATE_BYTE4<<24ul;
		AppConfig.PrimaryDNSServer.Val = MY_DEFAULT_PRIMARY_DNS_BYTE1 | MY_DEFAULT_PRIMARY_DNS_BYTE2<<8ul  | MY_DEFAULT_PRIMARY_DNS_BYTE3<<16ul  | MY_DEFAULT_PRIMARY_DNS_BYTE4<<24ul;
		AppConfig.SecondaryDNSServer.Val = MY_DEFAULT_SECONDARY_DNS_BYTE1 | MY_DEFAULT_SECONDARY_DNS_BYTE2<<8ul  | MY_DEFAULT_SECONDARY_DNS_BYTE3<<16ul  | MY_DEFAULT_SECONDARY_DNS_BYTE4<<24ul;
	
	
		// SNMP Community String configuration
		#if defined(STACK_USE_SNMP_SERVER)
		{
			BYTE i;
			static ROM char * ROM cReadCommunities[] = SNMP_READ_COMMUNITIES;
			static ROM char * ROM cWriteCommunities[] = SNMP_WRITE_COMMUNITIES;
			ROM char * strCommunity;
			
			for(i = 0; i < SNMP_MAX_COMMUNITY_SUPPORT; i++)
			{
				// Get a pointer to the next community string
				strCommunity = cReadCommunities[i];
				if(i >= sizeof(cReadCommunities)/sizeof(cReadCommunities[0]))
					strCommunity = "";
	
				// Ensure we don't buffer overflow.  If your code gets stuck here, 
				// it means your SNMP_COMMUNITY_MAX_LEN definition in TCPIPConfig.h 
				// is either too small or one of your community string lengths 
				// (SNMP_READ_COMMUNITIES) are too large.  Fix either.
				if(strlenpgm(strCommunity) >= sizeof(AppConfig.readCommunity[0]))
					while(1);
				
				// Copy string into AppConfig
				strcpypgm2ram((char*)AppConfig.readCommunity[i], strCommunity);
	
				// Get a pointer to the next community string
				strCommunity = cWriteCommunities[i];
				if(i >= sizeof(cWriteCommunities)/sizeof(cWriteCommunities[0]))
					strCommunity = "";
	
				// Ensure we don't buffer overflow.  If your code gets stuck here, 
				// it means your SNMP_COMMUNITY_MAX_LEN definition in TCPIPConfig.h 
				// is either too small or one of your community string lengths 
				// (SNMP_WRITE_COMMUNITIES) are too large.  Fix either.
				if(strlenpgm(strCommunity) >= sizeof(AppConfig.writeCommunity[0]))
					while(1);
	
				// Copy string into AppConfig
				strcpypgm2ram((char*)AppConfig.writeCommunity[i], strCommunity);
			}
		}
		#endif
	
		// Load the default NetBIOS Host Name
		memcpypgm2ram(AppConfig.NetBIOSName, (ROM void*)MY_DEFAULT_HOST_NAME, 16);
		FormatNetBIOSName(AppConfig.NetBIOSName);
	
		#if defined(WF_CS_TRIS)
			// Load the default SSID Name
			WF_ASSERT(sizeof(MY_DEFAULT_SSID_NAME) <= sizeof(AppConfig.MySSID));
			memcpypgm2ram(AppConfig.MySSID, (ROM void*)MY_DEFAULT_SSID_NAME, sizeof(MY_DEFAULT_SSID_NAME));
			AppConfig.SsidLength = sizeof(MY_DEFAULT_SSID_NAME) - 1;
	
	        AppConfig.SecurityMode = MY_DEFAULT_WIFI_SECURITY_MODE;
	        AppConfig.WepKeyIndex  = MY_DEFAULT_WEP_KEY_INDEX;
	        
	        #if (MY_DEFAULT_WIFI_SECURITY_MODE == WF_SECURITY_OPEN)
	            memset(AppConfig.SecurityKey, 0x00, sizeof(AppConfig.SecurityKey));
	            AppConfig.SecurityKeyLength = 0;
	
	        #elif MY_DEFAULT_WIFI_SECURITY_MODE == WF_SECURITY_WEP_40
	            memcpypgm2ram(AppConfig.SecurityKey, (ROM void*)MY_DEFAULT_WEP_KEYS_40, sizeof(MY_DEFAULT_WEP_KEYS_40) - 1);
	            AppConfig.SecurityKeyLength = sizeof(MY_DEFAULT_WEP_KEYS_40) - 1;
	
	        #elif MY_DEFAULT_WIFI_SECURITY_MODE == WF_SECURITY_WEP_104
			    memcpypgm2ram(AppConfig.SecurityKey, (ROM void*)MY_DEFAULT_WEP_KEYS_104, sizeof(MY_DEFAULT_WEP_KEYS_104) - 1);
			    AppConfig.SecurityKeyLength = sizeof(MY_DEFAULT_WEP_KEYS_104) - 1;
	
	        #elif (MY_DEFAULT_WIFI_SECURITY_MODE == WF_SECURITY_WPA_WITH_KEY)       || \
	              (MY_DEFAULT_WIFI_SECURITY_MODE == WF_SECURITY_WPA2_WITH_KEY)      || \
	              (MY_DEFAULT_WIFI_SECURITY_MODE == WF_SECURITY_WPA_AUTO_WITH_KEY)
			    memcpypgm2ram(AppConfig.SecurityKey, (ROM void*)MY_DEFAULT_PSK, sizeof(MY_DEFAULT_PSK) - 1);
			    AppConfig.SecurityKeyLength = sizeof(MY_DEFAULT_PSK) - 1;
	
	        #elif (MY_DEFAULT_WIFI_SECURITY_MODE == WF_SECURITY_WPA_WITH_PASS_PHRASE)     || \
	              (MY_DEFAULT_WIFI_SECURITY_MODE == WF_SECURITY_WPA2_WITH_PASS_PHRASE)    || \
	              (MY_DEFAULT_WIFI_SECURITY_MODE == WF_SECURITY_WPA_AUTO_WITH_PASS_PHRASE)
	            memcpypgm2ram(AppConfig.SecurityKey, (ROM void*)MY_DEFAULT_PSK_PHRASE, sizeof(MY_DEFAULT_PSK_PHRASE) - 1);
	            AppConfig.SecurityKeyLength = sizeof(MY_DEFAULT_PSK_PHRASE) - 1;
	
	        #else 
	            #error "No security defined"
	        #endif /* MY_DEFAULT_WIFI_SECURITY_MODE */
	
		#endif

		// Compute the checksum of the AppConfig defaults as loaded from ROM
		wOriginalAppConfigChecksum = CalcIPChecksum((BYTE*)&AppConfig, sizeof(AppConfig));

		#if defined(EEPROM_CS_TRIS) || defined(SPIFLASH_CS_TRIS)
		{
			NVM_VALIDATION_STRUCT NVMValidationStruct;

			// Check to see if we have a flag set indicating that we need to 
			// save the ROM default AppConfig values.
			if(vNeedToSaveDefaults)
				SaveAppConfig(&AppConfig);
		
			// Read the NVMValidation record and AppConfig struct out of EEPROM/Flash
			#if defined(EEPROM_CS_TRIS)
			{
				XEEReadArray(0x0000, (BYTE*)&NVMValidationStruct, sizeof(NVMValidationStruct));
				XEEReadArray(sizeof(NVMValidationStruct), (BYTE*)&AppConfig, sizeof(AppConfig));
			}
			#elif defined(SPIFLASH_CS_TRIS)
			{
				SPIFlashReadArray(0x0000, (BYTE*)&NVMValidationStruct, sizeof(NVMValidationStruct));
				SPIFlashReadArray(sizeof(NVMValidationStruct), (BYTE*)&AppConfig, sizeof(AppConfig));
			}
			#endif
	
			// Check EEPROM/Flash validitity.  If it isn't valid, set a flag so 
			// that we will save the ROM default values on the next loop 
			// iteration.
			if((NVMValidationStruct.wConfigurationLength != sizeof(AppConfig)) ||
			   (NVMValidationStruct.wOriginalChecksum != wOriginalAppConfigChecksum) ||
			   (NVMValidationStruct.wCurrentChecksum != CalcIPChecksum((BYTE*)&AppConfig, sizeof(AppConfig))))
			{
				// Check to ensure that the vNeedToSaveDefaults flag is zero, 
				// indicating that this is the first iteration through the do 
				// loop.  If we have already saved the defaults once and the 
				// EEPROM/Flash still doesn't pass the validity check, then it 
				// means we aren't successfully reading or writing to the 
				// EEPROM/Flash.  This means you have a hardware error and/or 
				// SPI configuration error.
				if(vNeedToSaveDefaults)
				{
					while(1);
				}
				
				// Set flag and restart loop to load ROM defaults and save them
				vNeedToSaveDefaults = 1;
				continue;
			}
			
			// If we get down here, it means the EEPROM/Flash has valid contents 
			// and either matches the ROM defaults or previously matched and 
			// was run-time reconfigured by the user.  In this case, we shall 
			// use the contents loaded from EEPROM/Flash.
			break;
		}
		#endif
		break;
	}
}

#if defined(EEPROM_CS_TRIS) || defined(SPIFLASH_CS_TRIS)
void SaveAppConfig(const APP_CONFIG *ptrAppConfig)
{
	NVM_VALIDATION_STRUCT NVMValidationStruct;

	// Ensure adequate space has been reserved in non-volatile storage to 
	// store the entire AppConfig structure.  If you get stuck in this while(1) 
	// trap, it means you have a design time misconfiguration in TCPIPConfig.h.
	// You must increase MPFS_RESERVE_BLOCK to allocate more space.
	#if defined(STACK_USE_MPFS2)
		if(sizeof(NVMValidationStruct) + sizeof(AppConfig) > MPFS_RESERVE_BLOCK)
			while(1);
	#endif

	// Get proper values for the validation structure indicating that we can use 
	// these EEPROM/Flash contents on future boot ups
	NVMValidationStruct.wOriginalChecksum = wOriginalAppConfigChecksum;
	NVMValidationStruct.wCurrentChecksum = CalcIPChecksum((BYTE*)ptrAppConfig, sizeof(APP_CONFIG));
	NVMValidationStruct.wConfigurationLength = sizeof(APP_CONFIG);

	// Write the validation struct and current AppConfig contents to EEPROM/Flash
	#if defined(EEPROM_CS_TRIS)
	    XEEBeginWrite(0x0000);
	    XEEWriteArray((BYTE*)&NVMValidationStruct, sizeof(NVMValidationStruct));
		XEEWriteArray((BYTE*)ptrAppConfig, sizeof(APP_CONFIG));
    #else
		SPIFlashBeginWrite(0x0000);
		SPIFlashWriteArray((BYTE*)&NVMValidationStruct, sizeof(NVMValidationStruct));
		SPIFlashWriteArray((BYTE*)ptrAppConfig, sizeof(APP_CONFIG));
    #endif
}
#endif
